MOSH-Insa-Toulouse/2025-2026-4GPa-Simonnet-Vidalenc/Images/[LTSpice] Amplificateur.png

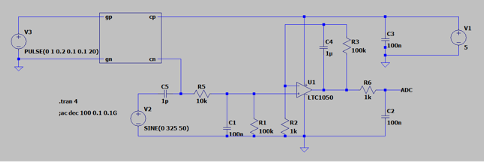
Images/[LTSpice] Amplificateur.png
