MOSH-Insa-Toulouse/2025-2026-4GPa-Simonnet-Vidalenc/Images/[PCB] Capteur graphite.png

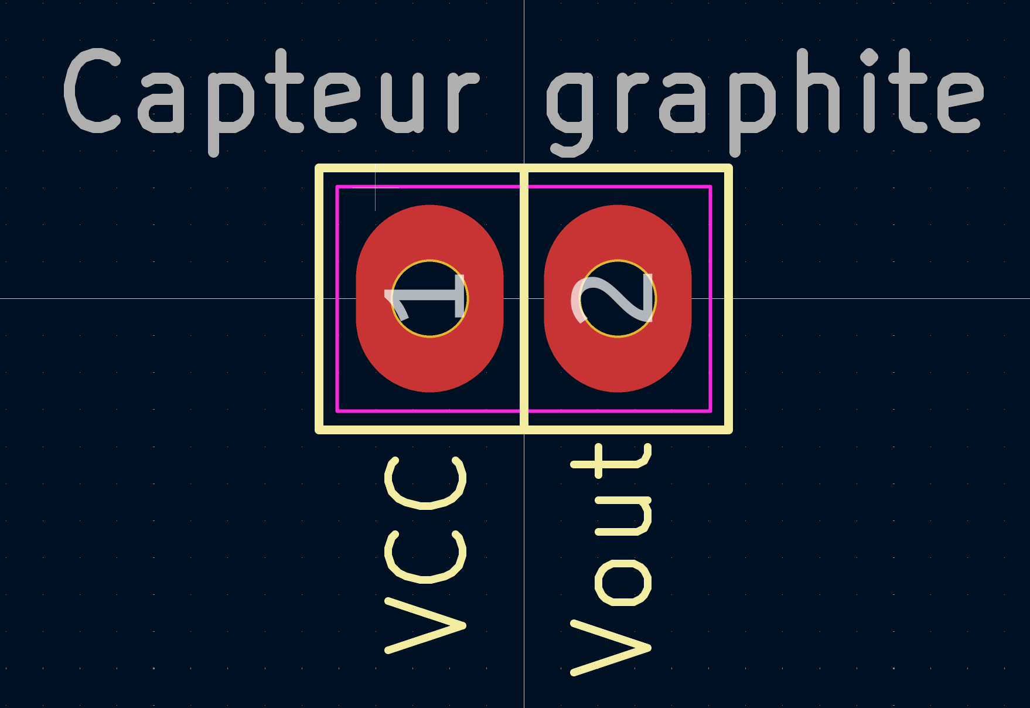
Images/[PCB] Capteur graphite.png
