MOSH-Insa-Toulouse/2025-2026-4GPa-Simonnet-Vidalenc/Images/[PCB] Condo 1u.png

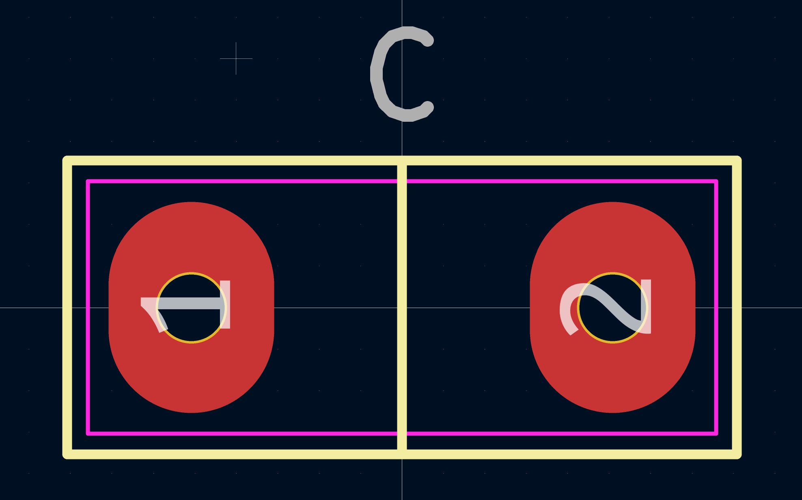
Images/[PCB] Condo 1u.png
