MOSH-Insa-Toulouse/2025-2026-4GPa-Simonnet-Vidalenc/Images/[SCH] Encodeur rotatoire.png

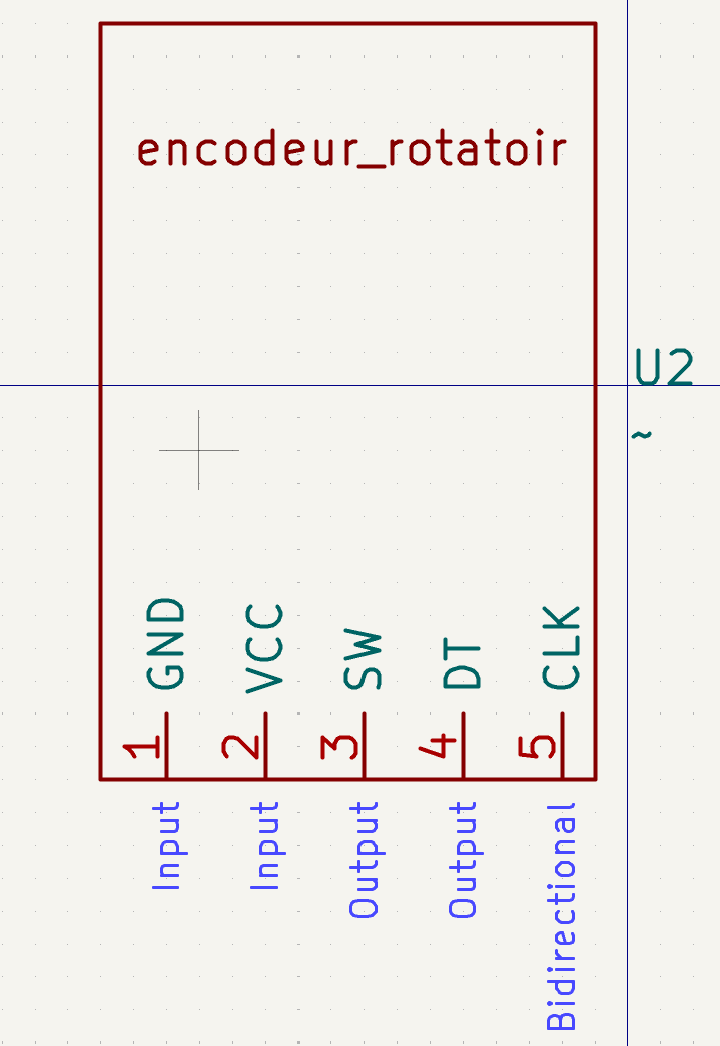
Images/[SCH] Encodeur rotatoire.png
