MOSH-Insa-Toulouse/2025-2026-4GPa-Simonnet-Vidalenc/Images/[SCH] Filtre et Ampli.png

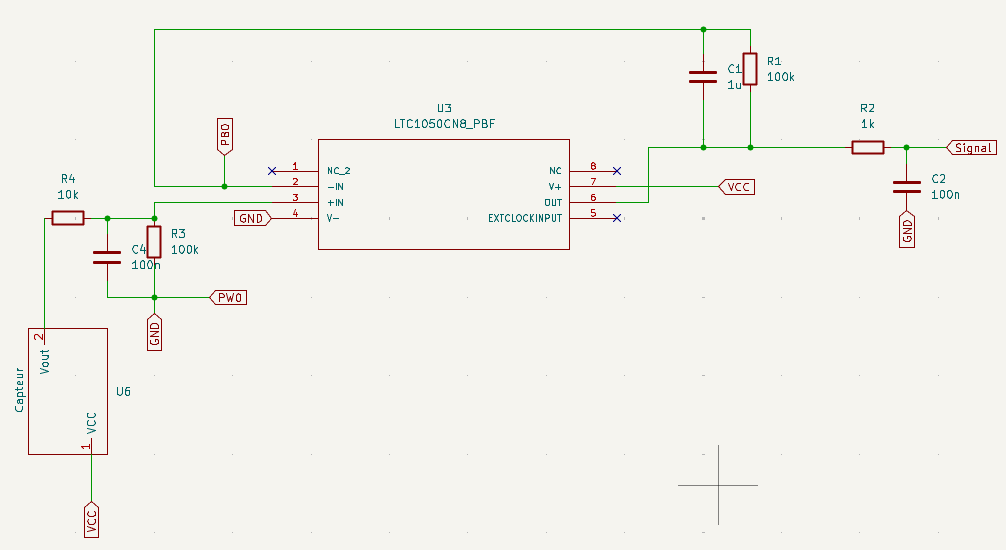
Images/[SCH] Filtre et Ampli.png
