MOSH-Insa-Toulouse/2025-2026-4GPa-Simonnet-Vidalenc/Images/[SCH] Servo-moteur.png

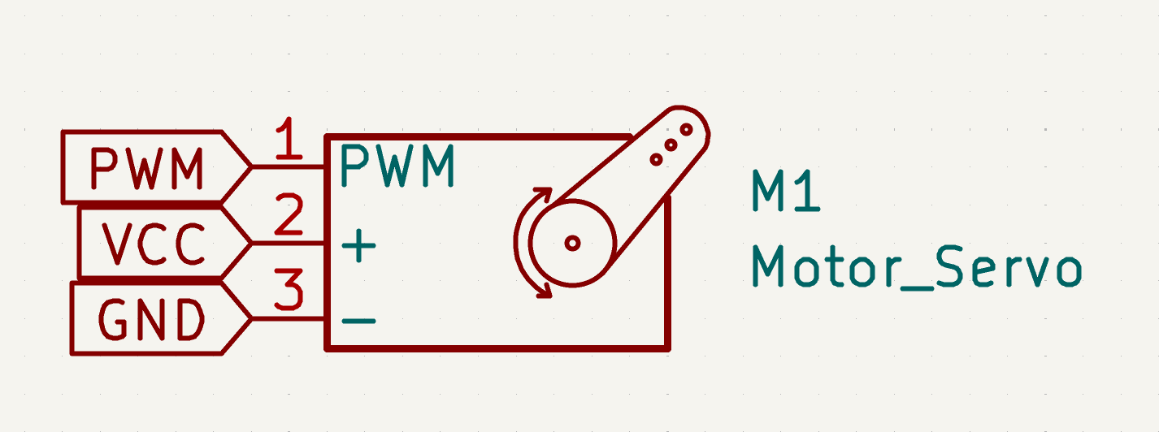
Images/[SCH] Servo-moteur.png
