MOSH-Insa-Toulouse/2025-2026-4GPa-Simonnet-Vidalenc/kicad-pcb-capteur-deformation/pin-header-female-2-54mm-different-pin-numbers-1.snapshot.4/2-Pin Header - Female - 2.54mm.step

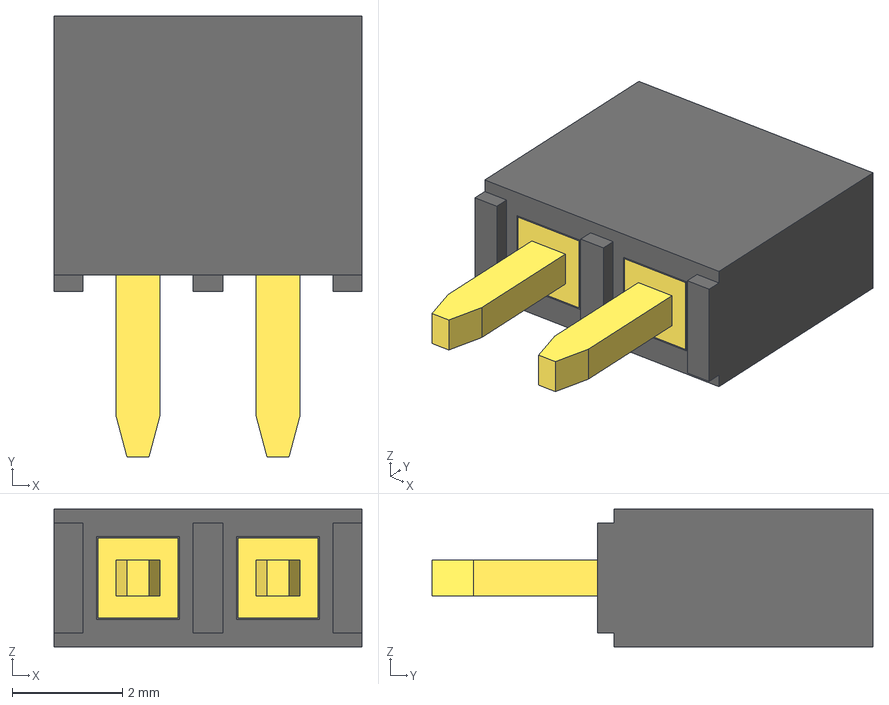
[picture p40: CAD file, 2026-02-11]
kicad-pcb-capteur-deformation/pin-header-female-2-54mm-different-pin-numbers-1.snapshot.4/2-Pin Header - Female - 2.54mm.step
5.58 x 8.00 x 2.50 mm
