MOSH-Insa-Toulouse/2025-2026-4GPa-Simonnet-Vidalenc/kicad-pcb-capteur-deformation/pin-header-female-2-54mm-different-pin-numbers-1.snapshot.4/5-Pin Header - Female - 2.54mm.step

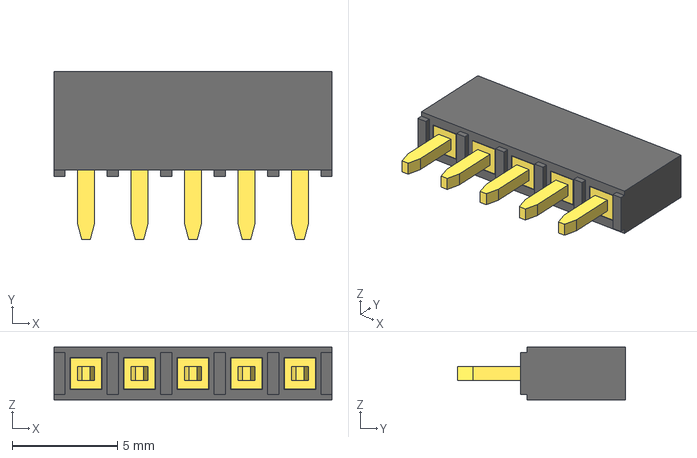
[picture p45: CAD file, 2026-02-11]
kicad-pcb-capteur-deformation/pin-header-female-2-54mm-different-pin-numbers-1.snapshot.4/5-Pin Header - Female - 2.54mm.step
13.2 x 8.00 x 2.50 mm
