MOSH-Insa-Toulouse/2025-2026-4GPa-Simonnet-Vidalenc/Images/[RESULTATS] Compression.png

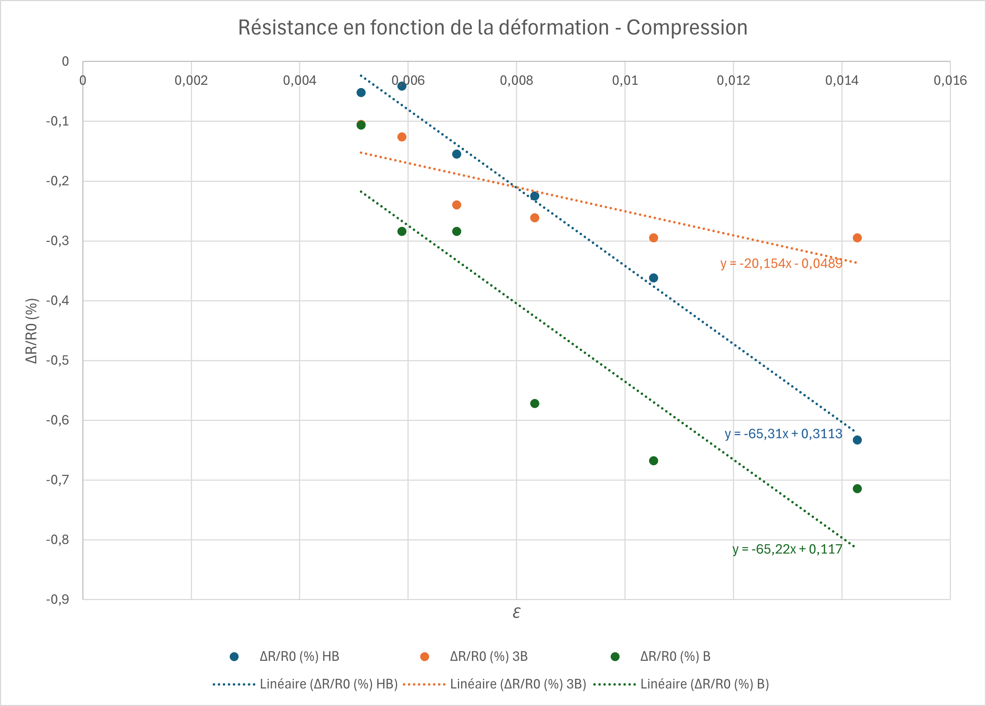
Images/[RESULTATS] Compression.png
