MOSH-Insa-Toulouse/2025-2026-4GPa-Simonnet-Vidalenc/Images/[RESULTATS] Traction.png

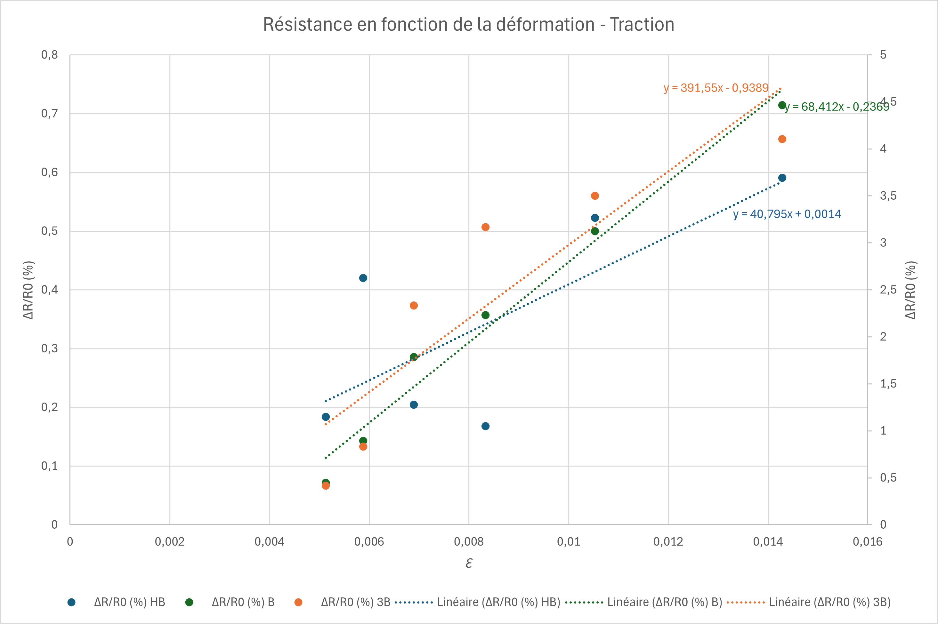
Images/[RESULTATS] Traction.png
